TAU-CGL/rplidar_recorder/cad/raw/raspberry-pi-4-model-b-8.snapshot.1/Raspberry Pi 4 Model B v2.png

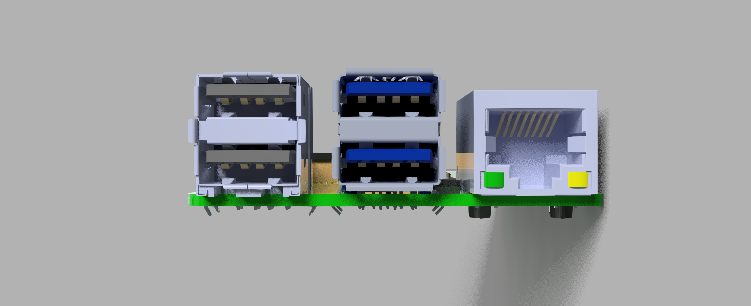
cad/raw/raspberry-pi-4-model-b-8.snapshot.1/Raspberry Pi 4 Model B v2.png
